ebastler/osprey/img/render_osprey_rev_a_top.png

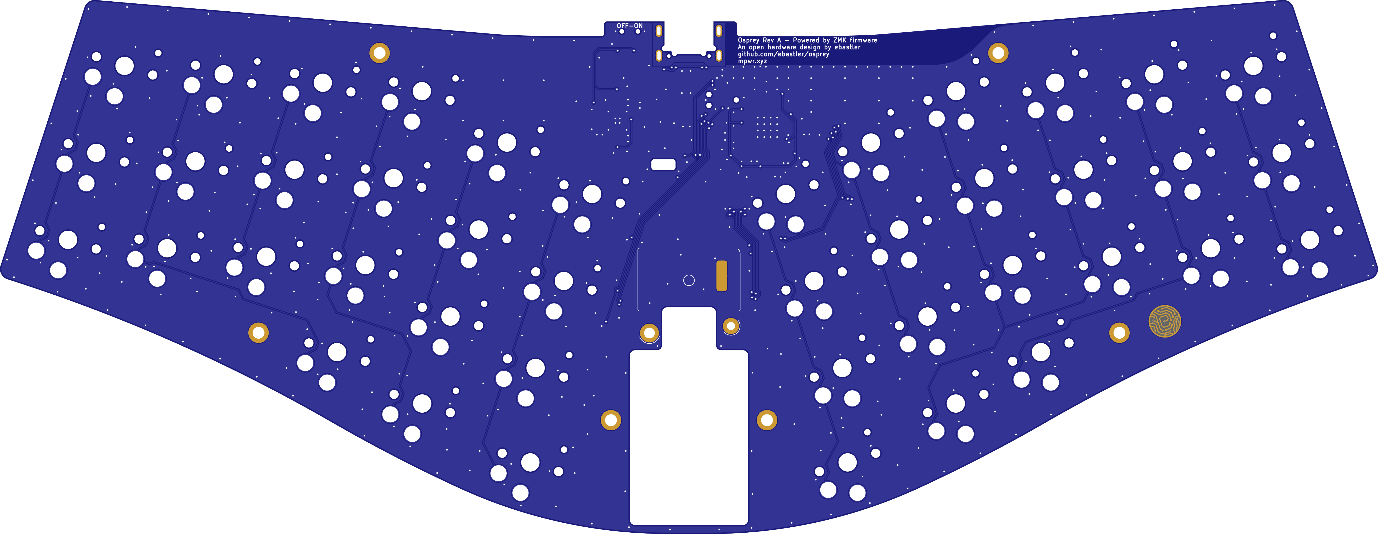
img/render_osprey_rev_a_top.png
