ebastler/osprey/osprey_plate/osprey_plate.kicad_sch

## KiCad design osprey_plate/osprey_plate.kicad_sch (2022-10-27)

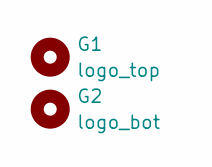
[picture p13: schematic osprey_plate.kicad_sch]

Parts:
G1: logo_top; logo_copper_7p5
G2: logo_bot; logo_copper_7p5
