ebastler/osprey/osprey_rev_a/osprey_rev_a.kicad_sch

## KiCad design osprey_rev_a/osprey_rev_a.kicad_sch (2022-10-27)

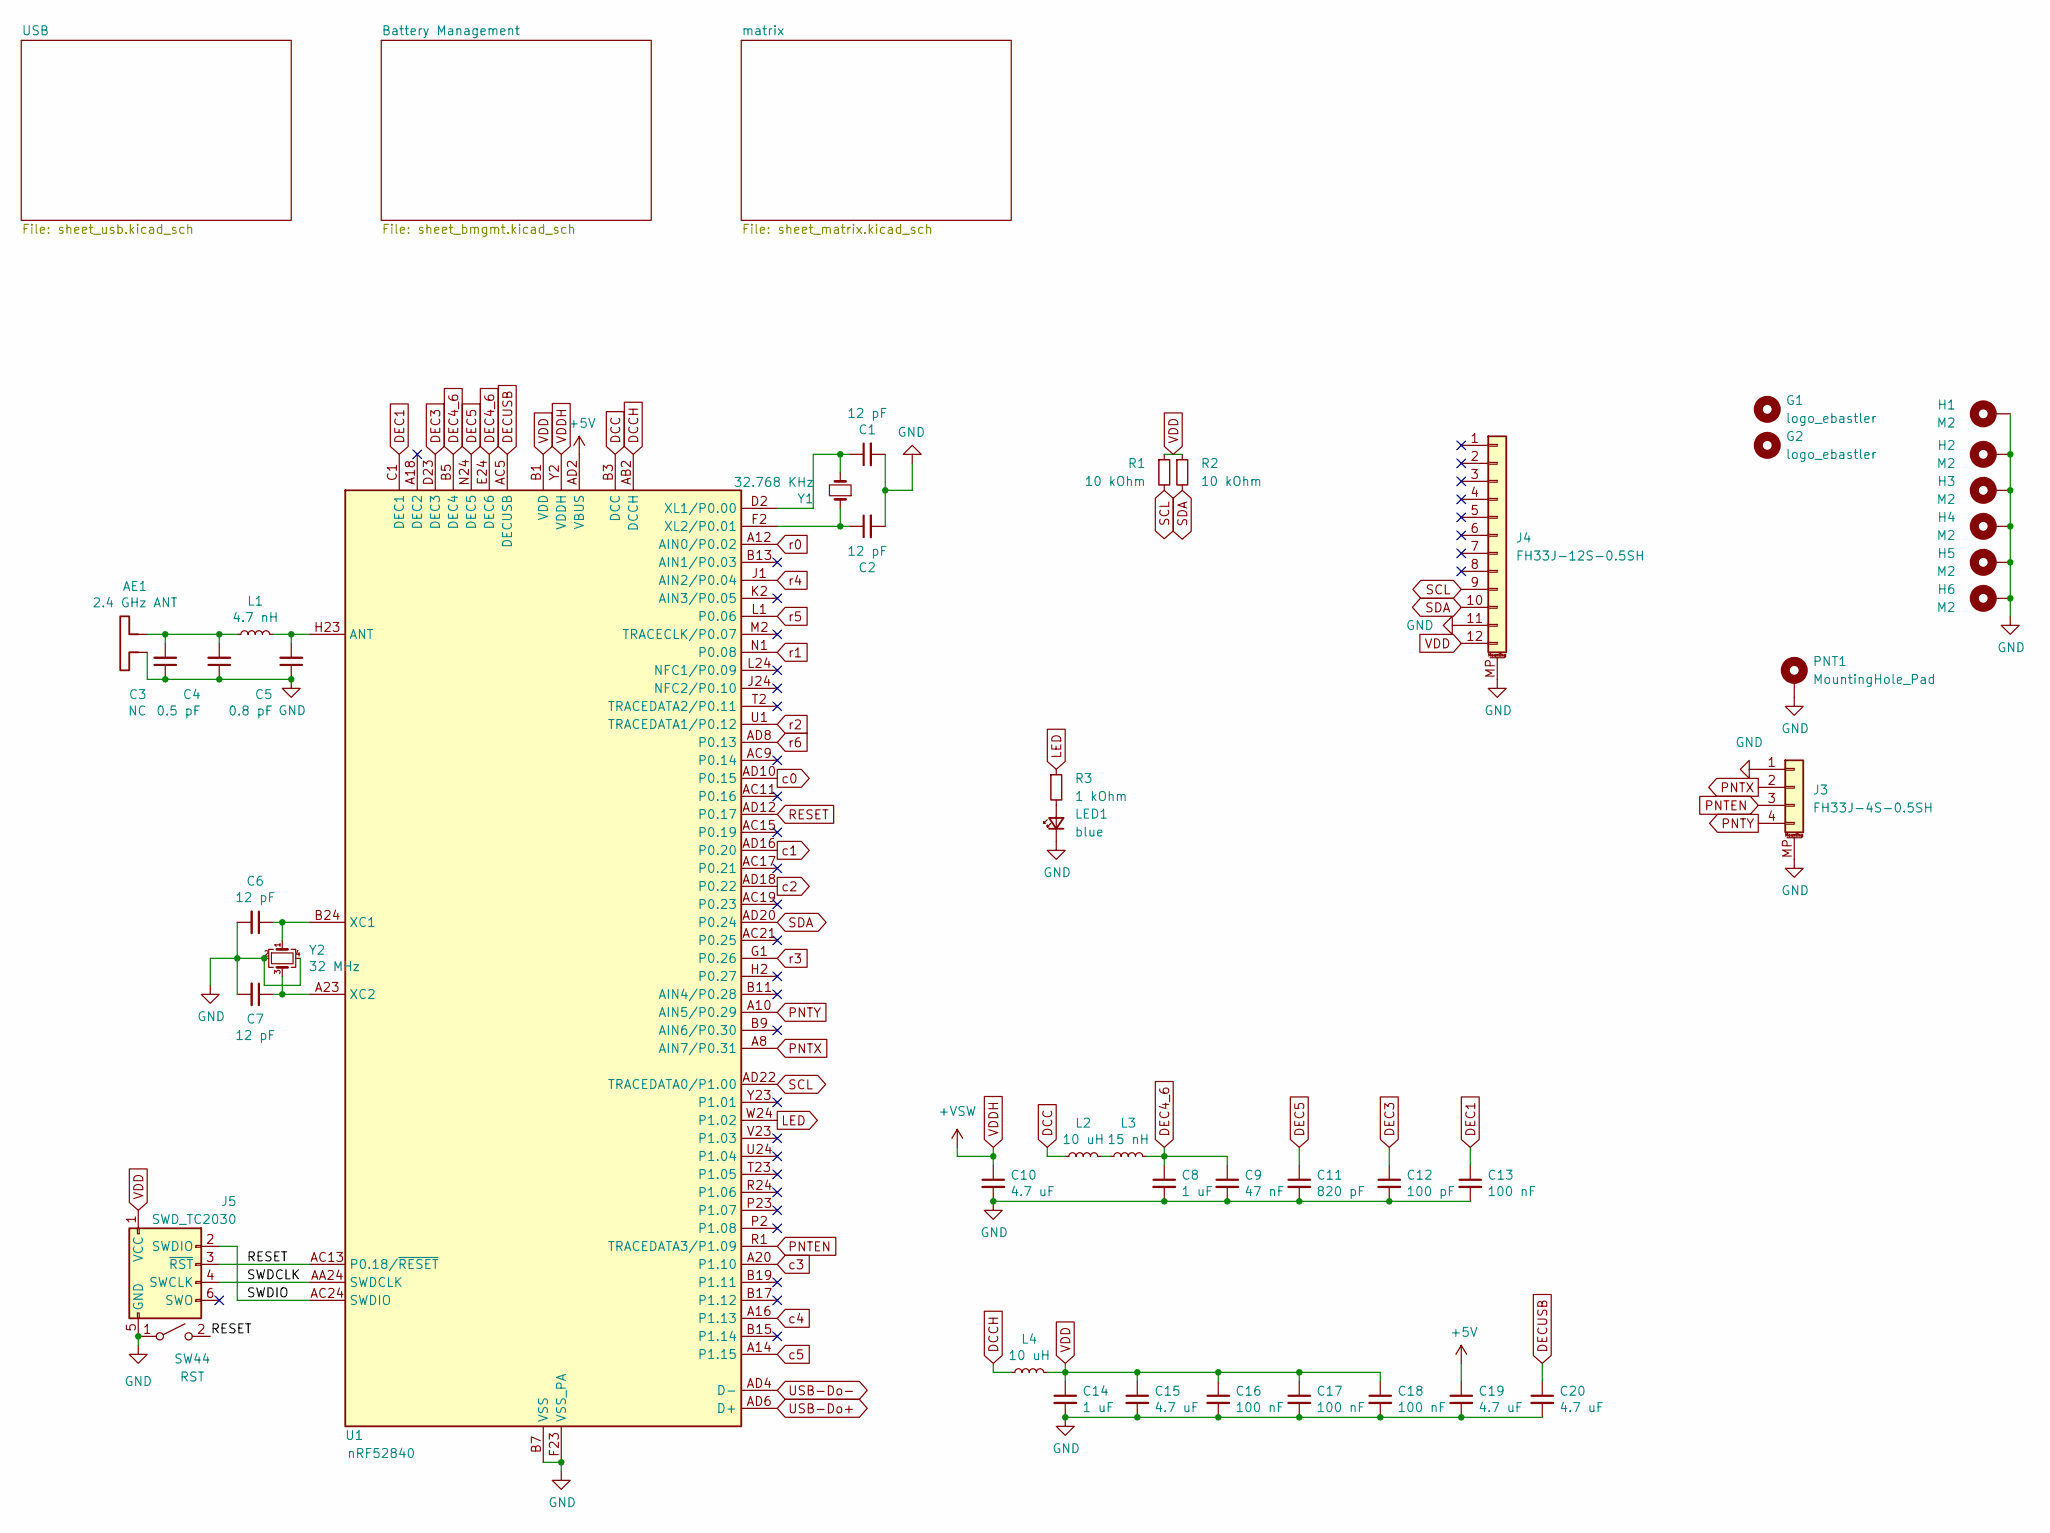
[picture p14: schematic osprey_rev_a.kicad_sch]

Parts:
AE1: 2.4 GHz ANT; Texas_SWRA117D_2.4GHz_Left
C1, C2, C6, C7: 12 pF; C_0402_1005Metric; LCSC C1547
C3: NC; C_0402_1005Metric; LCSC C77179
C4: 0.5 pF; C_0402_1005Metric; LCSC C77179
C5: 0.8 pF; C_0402_1005Metric; LCSC C285068
C8, C14: 1 uF; C_0402_1005Metric; LCSC C52923
C9: 47 nF; C_0402_1005Metric; LCSC C26403
C10, C15, C19, C20: 4.7 uF; C_0402_1005Metric; LCSC C23733
C11: 820 pF; C_0402_1005Metric; LCSC C161159
C12: 100 pF; C_0402_1005Metric; LCSC C1546
C13, C16, C17, C18: 100 nF; C_0402_1005Metric; LCSC C1525
G1, G2: logo_ebastler; logo_mask_6
H1, H2, H3, H4, H5, H6: M2; MountingHole_2.2mm_M2_DIN965_Pad
J3: FH33J-4S-0.5SH; CON_FH33J-4S-0.5SH
J4: FH33J-12S-0.5SH; CON_FH33J-12S-0.5SH
J5: SWD_TC2030; CON_TC2030_outlined
L1: 4.7 nH; L_0402_1005Metric; LCSC C251965
L2, L4: 10 uH; L_0603_1608Metric; LCSC C252081
L3: 15 nH; L_0402_1005Metric; LCSC C329619
LED1: blue; LED_0402_1005Metric; LCSC C72038
PNT1: MountingHole_Pad; PNT_RKJXU1210006
R1, R2: 10 kOhm; R_0402_1005Metric; LCSC C25744
R3: 1 kOhm; R_0402_1005Metric; LCSC C25890
SW44: RST; SW_SPST_SKQG_WithStem
U1: nRF52840; Nordic_AQFN-73-1EP_7x7mm_P0.5mm; LCSC C190794
Y1: 32.768 KHz; Crystal_SMD_2012-2Pin_2.0x1.2mm; LCSC C93231
Y2: 32 MHz; Crystal_SMD_2016-4Pin_2.0x1.6mm; LCSC C187794

Connections:
+5V: C19.1, U1.AD2 (VBUS)
+VSW: C10.1, U1.Y2 (VDDH)
DCC: L2.1, U1.B3 (DCC)
DCCH: L4.1, U1.AB2 (DCCH)
DEC1: C13.1, U1.C1 (DEC1)
DEC3: C12.1, U1.D23 (DEC3)
DEC4_6: C8.1, C9.1, L3.2, U1.B5 (DEC4), U1.E24 (DEC6)
DEC5: C11.1, U1.N24 (DEC5)
DECUSB: C20.1, U1.AC5 (DECUSB)
GND: AE1.2, C1.2, C2.2, C3.1, C4.1, C5.1, C6.2, C7.2, C8.2, C9.2, C10.2, C11.2, C12.2, C13.2, C14.2, C15.2, C16.2, C17.2, C18.2, C19.2, C20.2, H1.1, H2.1, H3.1, H4.1, H5.1, H6.1, J3.1, J3.MP (MountPin), J4.11, J4.MP (MountPin), J5.5 (GND), LED1.1 (K), PNT1.MP, SW44.1 (A), U1.B7 (VSS), U1.EP (VSS), U1.F23 (VSS_PA), Y2.2, Y2.4
LED: R3.1, U1.W24 (P1.02)
unnamed: AE1.1, C3.2, C4.2, L1.1
unnamed: C1.1, U1.D2 (XL1/P0.00), Y1.2
unnamed: C2.1, U1.F2 (XL2/P0.01), Y1.1
unnamed: C5.2, L1.2, U1.H23 (ANT)
unnamed: C6.1, U1.B24 (XC1), Y2.1
unnamed: C7.1, U1.A23 (XC2), Y2.3
unnamed: L2.2, L3.1
unnamed: LED1.2 (A), R3.2
PNTEN: J3.3, U1.R1 (TRACEDATA3/P1.09)
PNTX: J3.2, U1.A8 (AIN7/P0.31)
PNTY: J3.4, U1.A10 (AIN5/P0.29)
RESET: J5.3 (~RST), SW44.2 (B), U1.AC13 (P0.18/~RESET), U1.AD12 (P0.17)
SCL: J4.9, R1.2, U1.AD22 (TRACEDATA0/P1.00)
SDA: J4.10, R2.2, U1.AD20 (P0.24)
SWDCLK: J5.4 (SWCLK), U1.AA24 (SWDCLK)
SWDIO: J5.2 (SWDIO), U1.AC24 (SWDIO)
USB-Do+: U1.AD6 (D+)
USB-Do-: U1.AD4 (D-)
VDD: C14.1, C15.1, C16.1, C17.1, C18.1, J4.12, J5.1 (VCC), L4.2, R1.1, R2.1, U1.A22 (VDD), U1.AD14 (VDD), U1.AD23 (VDD), U1.B1 (VDD), U1.W1 (VDD)
c0: U1.AD10 (P0.15)
c1: U1.AD16 (P0.20)
c2: U1.AD18 (P0.22)
c3: U1.A20 (P1.10)
c4: U1.A16 (P1.13)
c5: U1.A14 (P1.15)
r0: U1.A12 (AIN0/P0.02)
r1: U1.N1 (P0.08)
r2: U1.U1 (TRACEDATA1/P0.12)
r3: U1.G1 (P0.26)
r4: U1.J1 (AIN2/P0.04)
r5: U1.L1 (P0.06)
r6: U1.AD8 (P0.13)
