ebastler/osprey/osprey_rev_a/sheet_bmgmt.kicad_sch

## KiCad design osprey_rev_a/sheet_bmgmt.kicad_sch (2022-10-27)

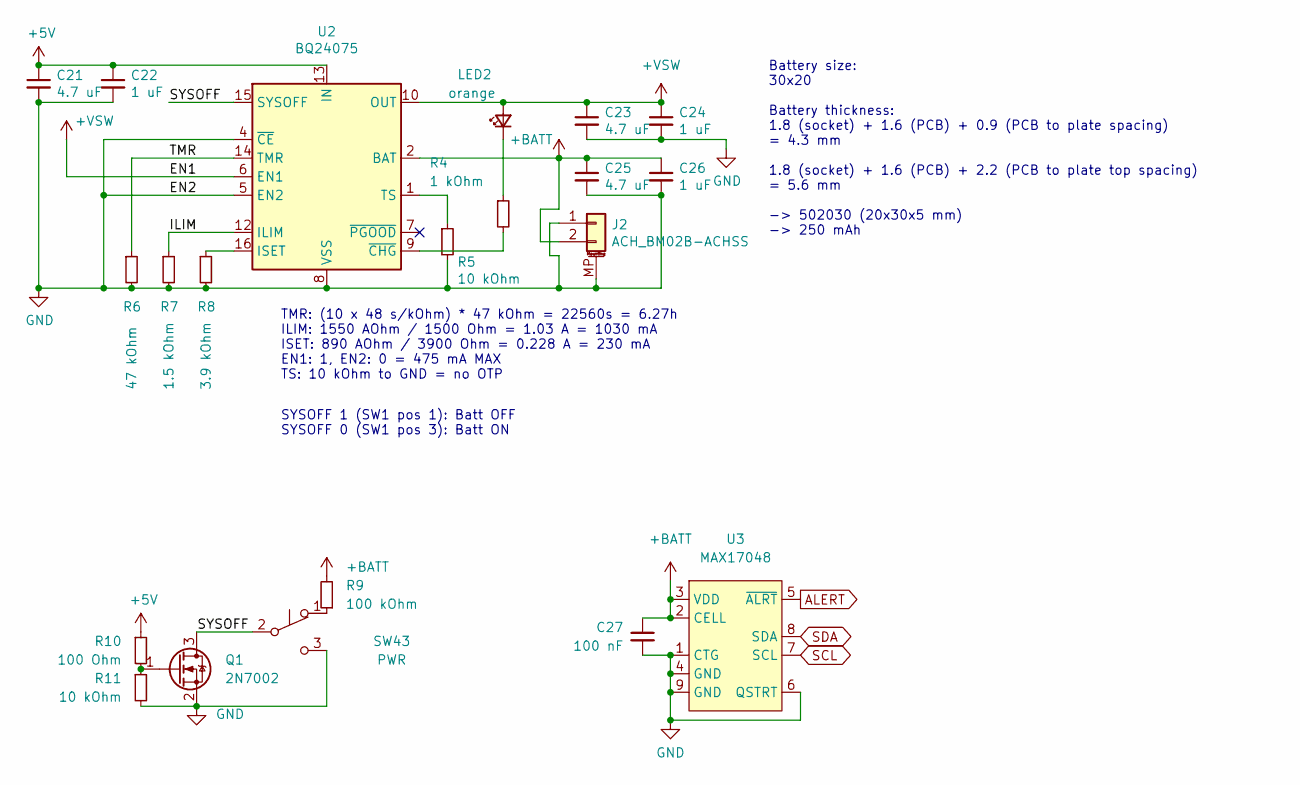
[picture p15: schematic sheet_bmgmt.kicad_sch]

Parts:
C21, C23, C25: 4.7 uF; C_0402_1005Metric; LCSC C23733
C22, C24, C26: 1 uF; C_0402_1005Metric; LCSC C52923
C27: 100 nF; C_0402_1005Metric
J2: ACH_BM02B-ACHSS; CON_JST_ACH_BM02B
LED2: orange; LED_0402_1005Metric; LCSC C72038
Q1: 2N7002; SOT-23
R4: 1 kOhm; R_0402_1005Metric; LCSC C25890
R5, R11: 10 kOhm; R_0402_1005Metric; LCSC C25744
R6: 47 kOhm; R_0402_1005Metric; LCSC C25792
R7: 1.5 kOhm; R_0402_1005Metric; LCSC C25867
R8: 3.9 kOhm; R_0402_1005Metric; LCSC C25744
R9: 100 kOhm; R_0402_1005Metric; LCSC C25744
R10: 100 Ohm; R_0402_1005Metric; LCSC C25744
SW43: PWR; SW_MSK12C02-HB
U2: BQ24075; VQFN-16-1EP_3x3mm_P0.5mm_EP1.6x1.6mm; LCSC C15464
U3: MAX17048; DFN-8-1EP_2x2mm_P0.5mm_EP0.7x1.3mm

Connections:
+5V: C21.1, C22.1, R10.1, U2.13 (IN)
+BATT: C25.1, C26.1, C27.1, J2.2, R9.2, U2.2 (BAT), U2.3 (BAT), U3.2 (CELL), U3.3 (VDD)
+VSW: C23.1, C24.1, LED2.2 (A), U2.6 (EN1), U2.10 (OUT), U2.11 (OUT)
ALERT: U3.5 (~ALRT)
GND: C21.2, C22.2, C23.2, C24.2, C25.2, C26.2, C27.2, J2.1, J2.MP (MountPin), Q1.2 (S), R5.2, R6.2, R7.2, R8.2, R11.2, SW43.3 (C), U2.4 (~CE), U2.5 (EN2), U2.8 (VSS), U2.17 (VSS), U3.1 (CTG), U3.4 (GND), U3.6 (QSTRT), U3.9 (GND)
ILIM: R7.1, U2.12 (ILIM)
unnamed: LED2.1 (K), R4.1
unnamed: Q1.1 (G), R10.2, R11.1
unnamed: R4.2, U2.9 (~CHG)
unnamed: R5.1, U2.1 (TS)
unnamed: R8.1, U2.16 (ISET)
unnamed: R9.1, SW43.1 (A)
SCL: U3.7 (SCL)
SDA: U3.8 (SDA)
SYSOFF: Q1.3 (D), SW43.2 (B), U2.15 (SYSOFF)
TMR: R6.1, U2.14 (TMR)

Notes on the sheet:
Battery size: 30x20 Battery thickness: 1.8 (socket) + 1.6 (PCB) + 0.9 (PCB to plate spacing) = 4.3 mm 1.8 (socket) + 1.6 (PCB) + 2.2 (PCB to plate top spacing) = 5.6 mm -> 502030 (20x30x5 mm) -> 250 mAh
TMR: (10 x 48 s/kOhm) * 47 kOhm = 22560s = 6.27h ILIM: 1550 AOhm / 1500 Ohm = 1.03 A = 1030 mA ISET: 890 AOhm / 3900 Ohm = 0.228 A = 230 mA EN1: 1, EN2: 0 = 475 mA MAX TS: 10 kOhm to GND = no OTP
SYSOFF 1 (SW1 pos 1): Batt OFF SYSOFF 0 (SW1 pos 3): Batt ON
