ebastler/osprey/osprey_rev_a/sheet_usb.kicad_sch

## KiCad design osprey_rev_a/sheet_usb.kicad_sch (2022-10-27)

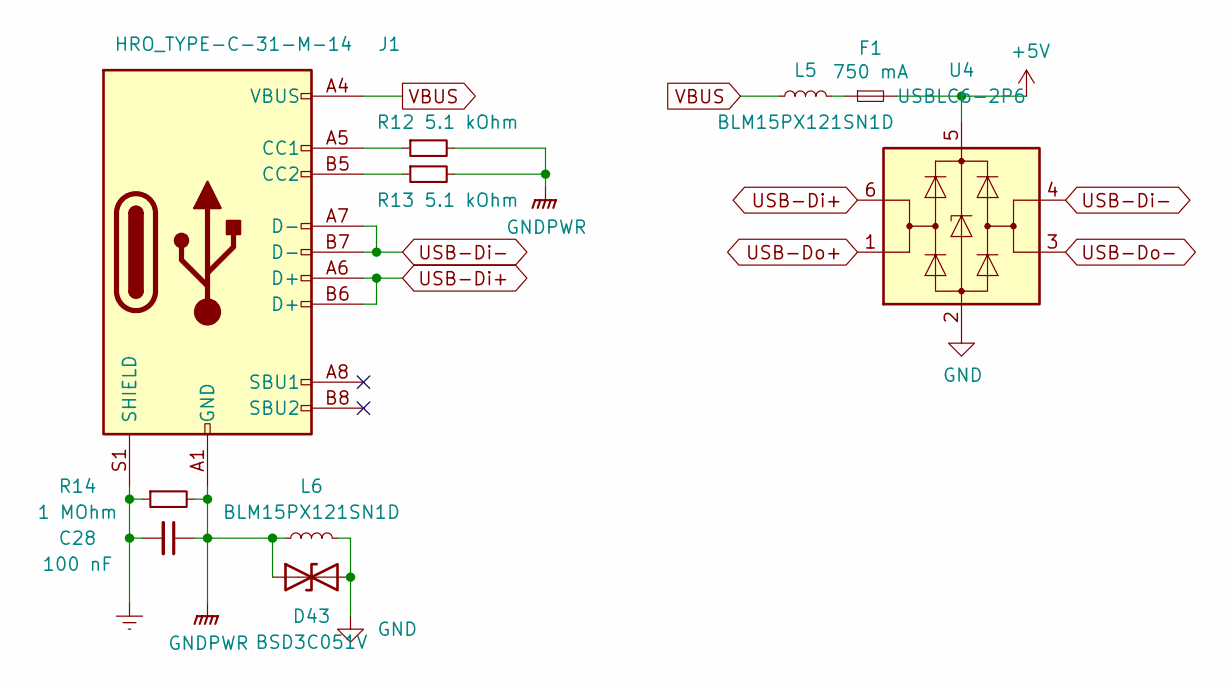
[picture p17: schematic sheet_usb.kicad_sch]

Parts:
C28: 100 nF; C_0402_1005Metric; LCSC C1525
D43: BSD3C051V; D_SOD-323; LCSC C151996
F1: 750 mA; Fuse_0603_1608Metric; LCSC C20792
J1: HRO_TYPE-C-31-M-14; USB_C_Receptacle_HRO_TYPE-C-31-M-14
L5, L6: BLM15PX121SN1D; L_0402_1005Metric; LCSC C88970
R12, R13: 5.1 kOhm; R_0402_1005Metric; LCSC C25905
R14: 1 MOhm; R_0402_1005Metric; LCSC C26083
U4: USBLC6-2P6; SOT-666; LCSC C15999

Connections:
+5V: F1.2, U4.5 (VBUS)
Earth: C28.2, J1.S1 (SHIELD), R14.1
GND: D43.2 (A2), L6.2, U4.2 (GND)
GNDPWR: C28.1, D43.1 (A1), J1.A1 (GND), J1.A12 (GND), J1.B1 (GND), J1.B12 (GND), L6.1, R12.2, R13.2, R14.2
unnamed: F1.1, L5.2
unnamed: J1.A5 (CC1), R12.1
unnamed: J1.B5 (CC2), R13.1
USB-Di+: J1.A6 (D+), J1.B6 (D+), U4.6 (I/O1)
USB-Di-: J1.A7 (D-), J1.B7 (D-), U4.4 (I/O2)
USB-Do+: U4.1 (I/O1)
USB-Do-: U4.3 (I/O2)
VBUS: J1.A4 (VBUS), J1.A9 (VBUS), J1.B4 (VBUS), J1.B9 (VBUS), L5.1
